Gaucho-Racing/Sensor-Nodes/Software/STM32G4/AIR SPEED/Core/Extras/VL53L4ED/platform.c

/**
  *
  * Copyright (c) 2023 STMicroelectronics.
  * All rights reserved.
  *
  * This software is licensed under terms that can be found in the LICENSE file
  * in the root directory of this software component.
  * If no LICENSE file comes with this software, it is provided AS-IS.
  *
  ******************************************************************************
  */

#include "platform.h"
#include "main.h"
#include "i2c.h"

extern I2C_HandleTypeDef hi2c1;


/*
Im legit just using the example stm provides but instead of filling everything out im only copying the platform.c implemintation
for the vl53l4ed sensor. 


*/

uint8_t VL53L4ED_RdDWord(Dev_t dev, uint16_t RegisterAdress, uint32_t *value)
{
	uint8_t status = 0;
	uint8_t data_write[2];
	uint8_t data_read[4];

	data_write[0] = (RegisterAdress >> 8) & 0xFF;
	data_write[1] = RegisterAdress & 0xFF;
	status = HAL_I2C_Master_Transmit(&hi2c1, dev, data_write, 2, 100);
	status = HAL_I2C_Master_Receive(&hi2c1, dev, data_read, 4, 100);
	*value =  ((data_read[0] << 24) | (data_read[1]<<16) |
			(data_read[2]<<8)| (data_read[3]));
	return status;
}

uint8_t VL53L4ED_RdWord(uint16_t dev, uint16_t RegisterAdress, uint16_t *value)
{
	uint8_t status = 0;
	uint8_t data_write[2];
	uint8_t data_read[2];

	data_write[0] = (RegisterAdress >> 8) & 0xFF;
	data_write[1] = RegisterAdress & 0xFF;
	status = HAL_I2C_Master_Transmit(&hi2c1, dev, data_write, 2, 100);
	status = HAL_I2C_Master_Receive(&hi2c1, dev, data_read, 2, 100);
	*value = (data_read[0] << 8) | (data_read[1]);
	return status;
}

uint8_t VL53L4ED_RdByte(uint16_t dev, uint16_t RegisterAdress, uint8_t *value)
{
	uint8_t status = 0;
	uint8_t data_write[2];
	uint8_t data_read[1];

	data_write[0] = (RegisterAdress >> 8) & 0xFF;
	data_write[1] = RegisterAdress & 0xFF;
	status = HAL_I2C_Master_Transmit(&hi2c1, dev, data_write, 2, 100);
	status = HAL_I2C_Master_Receive(&hi2c1, dev, data_read, 1, 100);
	*value = data_read[0];
	return status;
}

uint8_t VL53L4ED_WrByte(uint16_t dev, uint16_t RegisterAdress, uint8_t value)
{
	uint8_t data_write[3];
	uint8_t status = 0;

	data_write[0] = (RegisterAdress >> 8) & 0xFF;
	data_write[1] = RegisterAdress & 0xFF;
	data_write[2] = value & 0xFF;
	status = HAL_I2C_Master_Transmit(&hi2c1, dev, data_write, 3, 100);
	return status;
}

uint8_t VL53L4ED_WrWord(uint16_t dev, uint16_t RegisterAdress, uint16_t value)
{
	uint8_t data_write[4];
	uint8_t status = 0;
	data_write[0] = (RegisterAdress >> 8) & 0xFF;
	data_write[1] = RegisterAdress & 0xFF;
	data_write[2] = (value >> 8) & 0xFF;
	data_write[3] = value & 0xFF;
	status = HAL_I2C_Master_Transmit(&hi2c1, dev, data_write, 4, 100);
	return status;
}

uint8_t VL53L4ED_WrDWord(uint16_t dev, uint16_t RegisterAdress, uint32_t value)
{
	uint8_t data_write[6];
	uint8_t status = 0;

	data_write[0] = (RegisterAdress >> 8) & 0xFF;
	data_write[1] = RegisterAdress & 0xFF;
	data_write[2] = (value >> 24) & 0xFF;
	data_write[3] = (value >> 16) & 0xFF;
	data_write[4] = (value >> 8) & 0xFF;
	data_write[5] = value & 0xFF;
	status = HAL_I2C_Master_Transmit(&hi2c1, dev, data_write, 6, 100);
	return status;
}

uint8_t VL53L4ED_WaitMs(Dev_t dev, uint32_t time_ms)
{
	HAL_Delay(time_ms);
	return 0;
}
