Gaucho-Racing/Sensor-Nodes/Software/STM32G4/AIR SPEED/Core/Extras/VL53L4ED/platform.h

/**
  *
  * Copyright (c) 2023 STMicroelectronics.
  * All rights reserved.
  *
  * This software is licensed under terms that can be found in the LICENSE file
  * in the root directory of this software component.
  * If no LICENSE file comes with this software, it is provided AS-IS.
  *
  ******************************************************************************
  */

#ifndef _PLATFORM_H_
#define _PLATFORM_H_
#pragma once

#include <stdint.h>
#include <string.h>

/**
* VL53L4ED device instance.
*/

typedef uint16_t Dev_t;

/**
 * @brief Error instance.
 */
typedef uint8_t VL53L4ED_Error;

/**
 * @brief If the macro below is defined, the device will be programmed to run
 * with I2C Fast Mode Plus (up to 1MHz). Otherwise, default max value is 400kHz.
 */

//#define VL53L4ED_I2C_FAST_MODE_PLUS


/**
 * @brief Read 32 bits through I2C.
 */

uint8_t VL53L4ED_RdDWord(Dev_t dev, uint16_t registerAddr, uint32_t *value);
/**
 * @brief Read 16 bits through I2C.
 */

uint8_t VL53L4ED_RdWord(Dev_t dev, uint16_t registerAddr, uint16_t *value);

/**
 * @brief Read 8 bits through I2C.
 */

uint8_t VL53L4ED_RdByte(Dev_t dev, uint16_t registerAddr, uint8_t *value);

/**
 * @brief Write 8 bits through I2C.
 */

uint8_t VL53L4ED_WrByte(Dev_t dev, uint16_t registerAddr, uint8_t value);

/**
 * @brief Write 16 bits through I2C.
 */

uint8_t VL53L4ED_WrWord(Dev_t dev, uint16_t RegisterAdress, uint16_t value);

/**
 * @brief Write 32 bits through I2C.
 */

uint8_t VL53L4ED_WrDWord(Dev_t dev, uint16_t RegisterAdress, uint32_t value);

/**
 * @brief Wait during N milliseconds.
 */

uint8_t VL53L4ED_WaitMs(Dev_t dev, uint32_t TimeMs);

#endif	// _PLATFORM_H_
